weiserlab/MicroSymphony/Applications/HDC/hypercam_full_1536.h

#pragma once
#include <stdint.h>

#define HV_DIM_BITS   1536u
#define WORDS_PER_HV  48u
#define NUM_VALUE_HV  256u
#define NUM_CLASSES  10u
#define IMAGE_SIZE  784u

static const uint32_t X0_words[] = {
  1559332940, 2694472257, 3230908359, 2186010512, 3625210217, 3774503489, 3392811746, 113429167, 
  516840258, 3096450565, 1121410798, 3687732599, 2063754284, 2558345645, 2211788620, 4117558052, 
  1516208178, 753248, 1086007739, 3800809993, 3974189973, 3766735744, 1606023918, 2464322151, 
  18295811, 2987768501, 1385849143, 1591478497, 2674194754, 1576064407, 800652214, 4242529999, 
  3668197833, 3604213381, 3268835134, 668520246, 2330315098, 1921890300, 2413940358, 2788212711, 
  3203003012, 3453793345, 1027938997, 4056406996, 3236892148, 3991305691, 2264069579, 51414140, 

};

static const uint32_t value_hv[NUM_VALUE_HV][WORDS_PER_HV] = {
  {0, 0, 0, 0, 0, 0, 0, 0, 0, 0, 0, 0, 0, 0, 0, 0, 0, 0, 0, 0, 0, 0, 0, 0, 0, 0, 0, 0, 0, 0, 0, 0, 0, 0, 0, 0, 0, 0, 0, 0, 0, 0, 0, 0, 0, 0, 0, 0},
  {0, 0, 0, 0, 0, 0, 0, 131072, 0, 1, 0, 0, 0, 0, 0, 0, 0, 0, 0, 0, 0, 0, 0, 0, 32, 0, 2, 0, 0, 1024, 0, 0, 0, 0, 0, 0, 0, 0, 0, 0, 0, 0, 0, 65536, 0, 0, 0, 0},
  {0, 0, 0, 0, 0, 0, 0, 131072, 268435456, 1, 0, 0, 0, 0, 0, 0, 0, 0, 0, 0, 0, 0, 0, 0, 32, 0, 66, 0, 0, 1024, 0, 0, 0, 0, 0, 1, 0, 0, 33554432, 0, 0, 0, 4194304, 65536, 0, 0, 0, 64},
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
  0, 0, 0, 0, 0, 0, 0, 0, 0, 0, 0, 0, 3, 203, 254, 219, 
  35, 0, 0, 0, 0, 0, 0, 0, 0, 0, 0, 0, 0, 0, 0, 0, 
  0, 0, 0, 0, 0, 0, 0, 0, 38, 254, 254, 77, 0, 0, 0, 0, 
  0, 0, 0, 0, 0, 0, 0, 0, 0, 0, 0, 0, 0, 0, 0, 0, 
  0, 0, 0, 31, 224, 254, 115, 1, 0, 0, 0, 0, 0, 0, 0, 0, 
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

};
