weiserlab/MicroSymphony/Applications/HDC/hypercam_full_2304.h

#pragma once
#include <stdint.h>

#define HV_DIM_BITS   2304u
#define WORDS_PER_HV  72u
#define NUM_VALUE_HV  256u
#define NUM_CLASSES  10u
#define IMAGE_SIZE  784u

static const uint32_t X0_words[] = {
  4214503998, 546248404, 2707148496, 3777577888, 1912582900, 472547927, 640281245, 2200163611, 
  1401800407, 310445808, 730223411, 778288158, 1824375478, 2011415104, 2455839483, 3962809345, 
  2392819399, 1749167314, 3105747971, 1260189448, 3818951559, 1002261018, 3669284662, 3103818059, 
  3161772135, 3621505151, 4232781172, 2665584189, 3227941134, 2128598383, 2329596154, 4187344180, 
  956813356, 3261212595, 3201115846, 3319187049, 3497880699, 1375305694, 1904997709, 3522812471, 
  996184780, 2348785268, 4139385779, 3420244577, 4040491899, 3425927892, 4186174944, 1715335256, 
  514481378, 3260633653, 2604803211, 2552000822, 2605380143, 318495680, 3037816078, 895049210, 
  2887361740, 3337717783, 545751621, 4075105981, 1374854642, 2690008995, 1528891427, 281545589, 
  2535610143, 2332044382, 3550773132, 2409828395, 3662610843, 3424583193, 3007942292, 1598622558, 

};

static const uint32_t value_hv[NUM_VALUE_HV][WORDS_PER_HV] = {
  {0, 0, 0, 0, 0, 0, 0, 0, 0, 0, 0, 0, 0, 0, 0, 0, 0, 0, 0, 0, 0, 0, 0, 0, 0, 0, 0, 0, 0, 0, 0, 0, 0, 0, 0, 0, 0, 0, 0, 0, 0, 0, 0, 0, 0, 0, 0, 0, 0, 0, 0, 0, 0, 0, 0, 0, 0, 0, 0, 0, 0, 0, 0, 0, 0, 0, 0, 0, 0, 0, 0, 0},
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
  0, 0, 0, 0, 0, 0, 0, 0, 0, 0, 0, 0, 3, 203, 254, 219, 
  35, 0, 0, 0, 0, 0, 0, 0, 0, 0, 0, 0, 0, 0, 0, 0, 
  0, 0, 0, 0, 0, 0, 0, 0, 38, 254, 254, 77, 0, 0, 0, 0, 
  0, 0, 0, 0, 0, 0, 0, 0, 0, 0, 0, 0, 0, 0, 0, 0, 
  0, 0, 0, 31, 224, 254, 115, 1, 0, 0, 0, 0, 0, 0, 0, 0, 
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

};
