weiserlab/MicroSymphony/Applications/HDC/hypercam_full_256.h

#pragma once
#include <stdint.h>

#define HV_DIM_BITS   256u
#define WORDS_PER_HV  8u
#define NUM_VALUE_HV  256u
#define NUM_CLASSES  10u
#define IMAGE_SIZE  784u

static const uint32_t X0_words[] = {
  2025300114, 2783741248, 3952806378, 3305013273, 3534077634, 763819753, 845482458, 612500199, 

};

static const uint32_t value_hv[NUM_VALUE_HV][WORDS_PER_HV] = {
  {0, 0, 0, 0, 0, 0, 0, 0},
  {0, 0, 1048576, 0, 0, 0, 0, 0},
  {0, 0, 3145728, 0, 0, 0, 0, 0},
  {0, 262144, 3145728, 0, 0, 0, 0, 0},
  {0, 262144, 3145728, 0, 16, 0, 0, 0},
  {0, 262144, 3145760, 0, 16, 0, 0, 0},
  {0, 262144, 3145760, 0, 16, 0, 0, 536870912},
  {0, 262272, 3145760, 0, 16, 0, 0, 536870912},
  {0, 262272, 3145760, 0, 16, 64, 0, 536870912},
  {0, 262272, 3145760, 0, 16, 64, 32768, 536870912},
  {0, 327808, 3145760, 0, 16, 64, 32768, 536870912},
  {0, 327808, 3146784, 0, 16, 64, 32768, 536870912},
  {8388608, 327808, 3146784, 0, 16, 64, 32768, 536870912},
  {8388608, 327808, 3146784, 134217728, 16, 64, 32768, 536870912},
  {8388608, 327808, 3146784, 134217728, 16, 64, 1081344, 536870912},
  {8388608, 327808, 3146784, 134217729, 16, 64, 1081344, 536870912},
  {8388608, 327808, 3146784, 134225921, 16, 64, 1081344, 536870912},
  {8388608, 327808, 3146784, 134225921, 16, 2097216, 1081344, 536870912},
  {2155872256, 327808, 3146784, 134225921, 16, 2097216, 1081344, 536870912},
  {2155937792, 327808, 3146784, 134225921, 16, 2097216, 1081344, 536870912},
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
  0, 0, 0, 0, 133, 254, 187, 5, 0, 0, 0, 0, 0, 0, 0, 0, 
  0, 0, 0, 0, 0, 0, 0, 0, 0, 0, 0, 0, 0, 0, 0, 9, 
  205, 248, 58, 0, 0, 0, 0, 0, 0, 0, 0, 0, 0, 0, 0, 0, 
  0, 0, 0, 0, 0, 0, 0, 0, 0, 0, 0, 126, 254, 182, 0, 0, 
  0, 0, 0, 0, 0, 0, 0, 0, 0, 0, 0, 0, 0, 0, 0, 0, 
  0, 0, 0, 0, 0, 0, 75, 251, 240, 57, 0, 0, 0, 0, 0, 0, 
  0, 0, 0, 0, 0, 0, 0, 0, 0, 0, 0, 0, 0, 0, 0, 0, 
  0, 19, 221, 254, 166, 0, 0, 0, 0, 0, 0, 0, 0, 0, 0, 0, 
  0, 0, 0, 0, 0, 0, 0, 0, 0, 0, 0, 0, 3, 203, 254, 219, 
  35, 0, 0, 0, 0, 0, 0, 0, 0, 0, 0, 0, 0, 0, 0, 0, 
  0, 0, 0, 0, 0, 0, 0, 0, 38, 254, 254, 77, 0, 0, 0, 0, 
  0, 0, 0, 0, 0, 0, 0, 0, 0, 0, 0, 0, 0, 0, 0, 0, 
  0, 0, 0, 31, 224, 254, 115, 1, 0, 0, 0, 0, 0, 0, 0, 0, 
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

};
