weiserlab/MicroSymphony/Applications/HDC/hypercam_full_512.h

#pragma once
#include <stdint.h>

#define HV_DIM_BITS   512u
#define WORDS_PER_HV  16u
#define NUM_VALUE_HV  256u
#define NUM_CLASSES  10u
#define IMAGE_SIZE  784u

static const uint32_t X0_words[] = {
  6052134, 3420975704, 1169717759, 1064196224, 1859324112, 1284353818, 3406143220, 2119787277, 
  2780352291, 2795643669, 607298185, 2134716628, 2701171630, 387996285, 2135934987, 2162884167, 

};

static const uint32_t value_hv[NUM_VALUE_HV][WORDS_PER_HV] = {
  {0, 0, 0, 0, 0, 0, 0, 0, 0, 0, 0, 0, 0, 0, 0, 0},
  {0, 0, 0, 0, 524288, 0, 0, 0, 0, 0, 0, 0, 0, 16777216, 0, 0},
  {0, 0, 0, 0, 524288, 0, 0, 0, 0, 0, 0, 33554432, 0, 16777280, 0, 0},
  {0, 536870912, 0, 0, 524288, 0, 4194304, 0, 0, 0, 0, 33554432, 0, 16777280, 0, 0},
  {0, 536870912, 0, 0, 524288, 0, 4194304, 2048, 0, 0, 0, 33554432, 0, 16777280, 0, 4194304},
  {0, 536870912, 0, 0, 524288, 0, 4194306, 2048, 0, 0, 0, 33554432, 1073741824, 16777280, 0, 4194304},
  {0, 536870912, 2048, 0, 524288, 0, 4194306, 2099200, 0, 0, 0, 33554432, 1073741824, 16777280, 0, 4194304},
  {0, 536870912, 2048, 131072, 524288, 0, 4194306, 2099200, 0, 0, 16, 33554432, 1073741824, 16777280, 0, 4194304},
  {0, 537133056, 2048, 131072, 589824, 0, 4194306, 2099200, 0, 0, 16, 33554432, 1073741824, 16777280, 0, 4194304},
  {4, 537133056, 2048, 131072, 589824, 0, 4194306, 2099200, 0, 0, 16, 33554432, 1073741824, 16777280, 2147483648, 4194304},
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
  0, 0, 0, 0, 0, 0, 0, 0, 0, 0, 0, 0, 3, 203, 254, 219, 
  35, 0, 0, 0, 0, 0, 0, 0, 0, 0, 0, 0, 0, 0, 0, 0, 
  0, 0, 0, 0, 0, 0, 0, 0, 38, 254, 254, 77, 0, 0, 0, 0, 
  0, 0, 0, 0, 0, 0, 0, 0, 0, 0, 0, 0, 0, 0, 0, 0, 
  0, 0, 0, 31, 224, 254, 115, 1, 0, 0, 0, 0, 0, 0, 0, 0, 
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

};
