weiserlab/MicroSymphony/Applications/HDC/hypercam_full_768.h

#pragma once
#include <stdint.h>

#define HV_DIM_BITS   768u
#define WORDS_PER_HV  24u
#define NUM_VALUE_HV  256u
#define NUM_CLASSES  10u
#define IMAGE_SIZE  784u

static const uint32_t X0_words[] = {
  4137574202, 4070408322, 3817061801, 1278804884, 2879217275, 3336658757, 2747441063, 1155029396, 
  2571989088, 223358262, 3187925497, 11351408, 1837061471, 1510557048, 3848276927, 3274084819, 
  411392216, 597666974, 4159650377, 519449597, 1180059248, 4104064114, 2962328063, 1551634708, 

};

static const uint32_t value_hv[NUM_VALUE_HV][WORDS_PER_HV] = {
  {0, 0, 0, 0, 0, 0, 0, 0, 0, 0, 0, 0, 0, 0, 0, 0, 0, 0, 0, 0, 0, 0, 0, 0},
  {0, 4194304, 0, 0, 0, 32768, 0, 0, 0, 0, 0, 0, 0, 0, 0, 0, 0, 0, 0, 0, 0, 16777216, 0, 0},
  {8192, 4194304, 16384, 0, 0, 34816, 0, 0, 0, 0, 0, 0, 0, 0, 0, 0, 0, 0, 0, 0, 0, 16777216, 0, 0},
  {8192, 4194304, 16384, 0, 512, 8423424, 0, 0, 524288, 0, 0, 0, 0, 0, 0, 0, 0, 0, 0, 0, 0, 16777216, 0, 0},
  {8192, 4194304, 16384, 0, 512, 8947712, 0, 0, 524288, 0, 0, 0, 0, 0, 0, 0, 0, 0, 536870944, 0, 0, 16777216, 0, 0},
  {8192, 4194304, 16384, 0, 8389120, 8947712, 0, 0, 524288, 0, 0, 131072, 0, 0, 0, 0, 0, 0, 536870944, 0, 0, 16777218, 0, 0},
  {8192, 4194304, 81920, 0, 8389120, 8947712, 0, 0, 524288, 0, 0, 131072, 67108864, 0, 0, 0, 0, 0, 536870944, 134217728, 0, 16777218, 0, 0},
  {8192, 4194320, 81920, 131072, 8389120, 8947712, 0, 0, 524288, 0, 0, 131072, 67108864, 0, 0, 0, 0, 1073741824, 536870944, 134217728, 0, 16777218, 0, 0},
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
  0, 0, 0, 0, 0, 0, 0, 0, 0, 0, 0, 0, 3, 203, 254, 219, 
  35, 0, 0, 0, 0, 0, 0, 0, 0, 0, 0, 0, 0, 0, 0, 0, 
  0, 0, 0, 0, 0, 0, 0, 0, 38, 254, 254, 77, 0, 0, 0, 0, 
  0, 0, 0, 0, 0, 0, 0, 0, 0, 0, 0, 0, 0, 0, 0, 0, 
  0, 0, 0, 31, 224, 254, 115, 1, 0, 0, 0, 0, 0, 0, 0, 0, 
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

};
